Tirthak-bot/Tamagotchi/PCB/Tamagotchi PCB.png

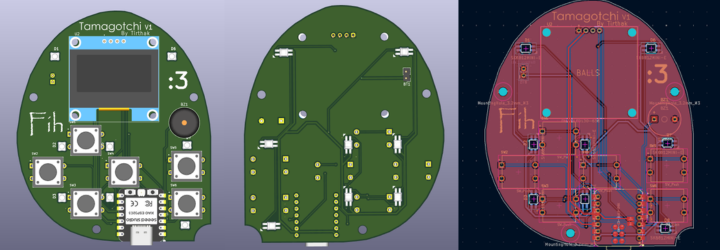
PCB/Tamagotchi PCB.png
