Tirthak-bot/Tamagotchi/Renders/IRL Images/IMG_20260520_202827706 (1).jpg

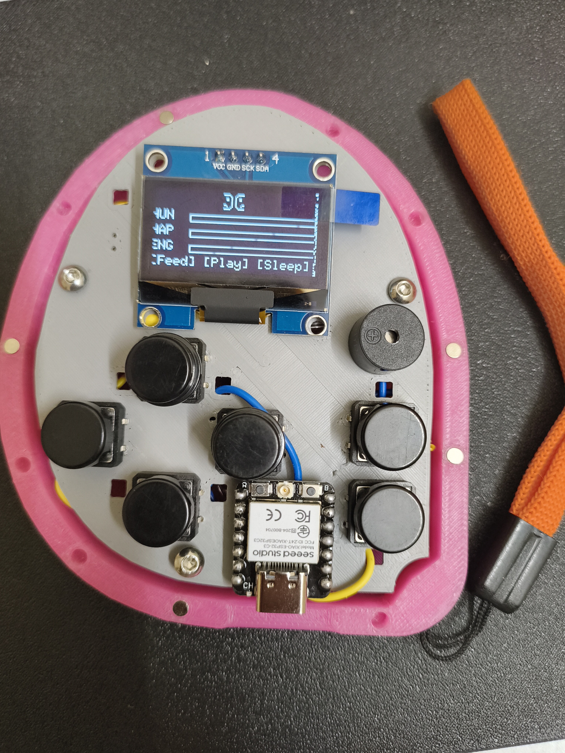
Renders/IRL Images/IMG_20260520_202827706 (1).jpg
