Tirthak-bot/Tamagotchi/Renders/IRL Images/IMG_20260521_135610531.jpg

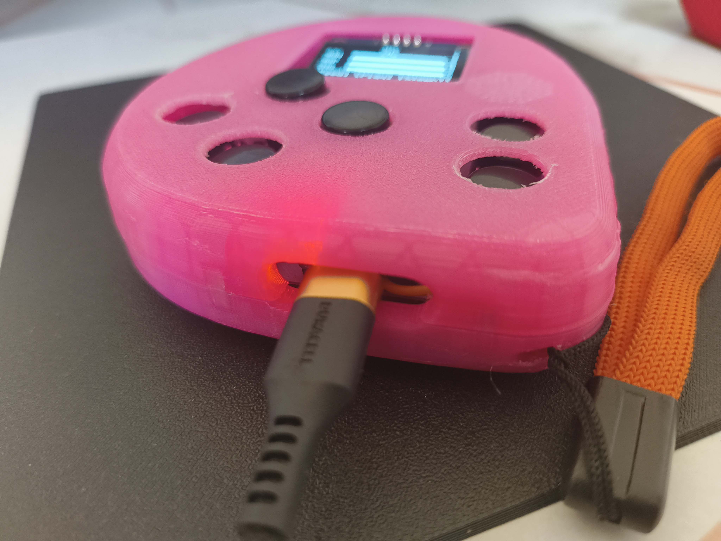
Renders/IRL Images/IMG_20260521_135610531.jpg
