Tirthak-bot/Tamagotchi/Renders/Render 1.png

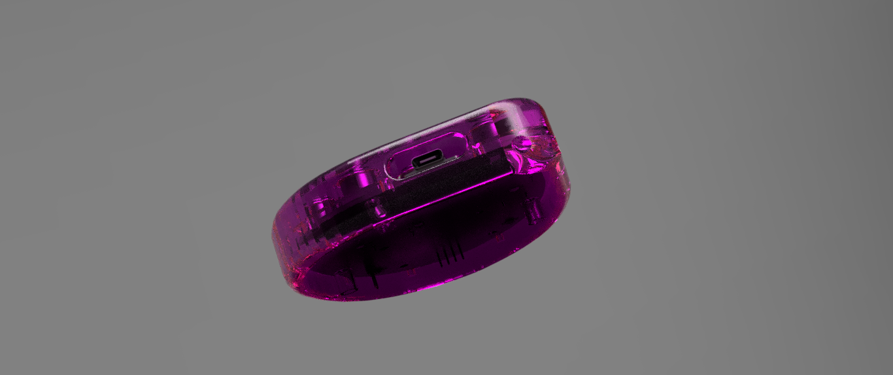
Renders/Render 1.png
