Tirthak-bot/Tamagotchi/Renders/Render Compilation.png

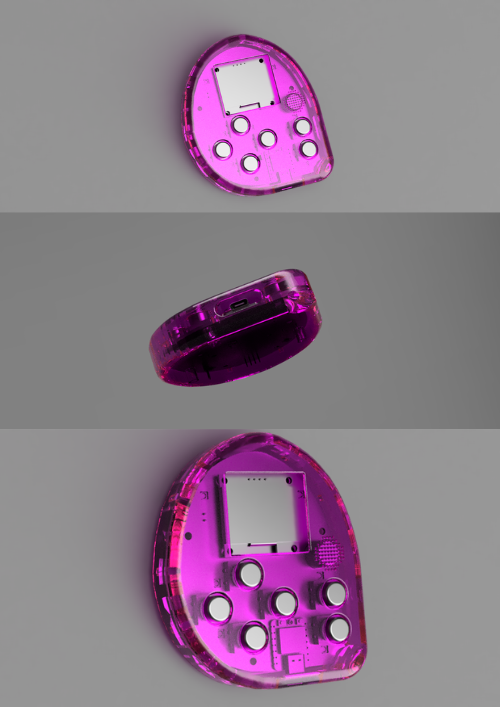
Renders/Render Compilation.png
