Tirthak-bot/Tamagotchi/Renders/Tamagotchi Zine Page With IRL Image.png

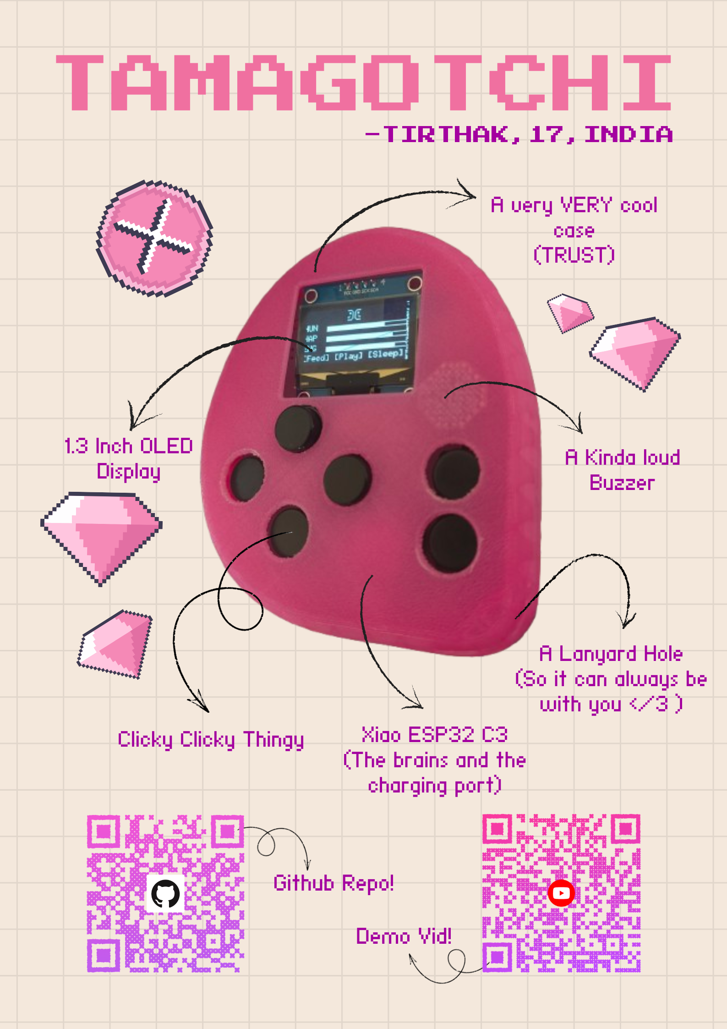
Renders/Tamagotchi Zine Page With IRL Image.png
